BlackbirdStandalone/ToothEater-HW-THT/pcb/BOM/v1.1/BOM.png

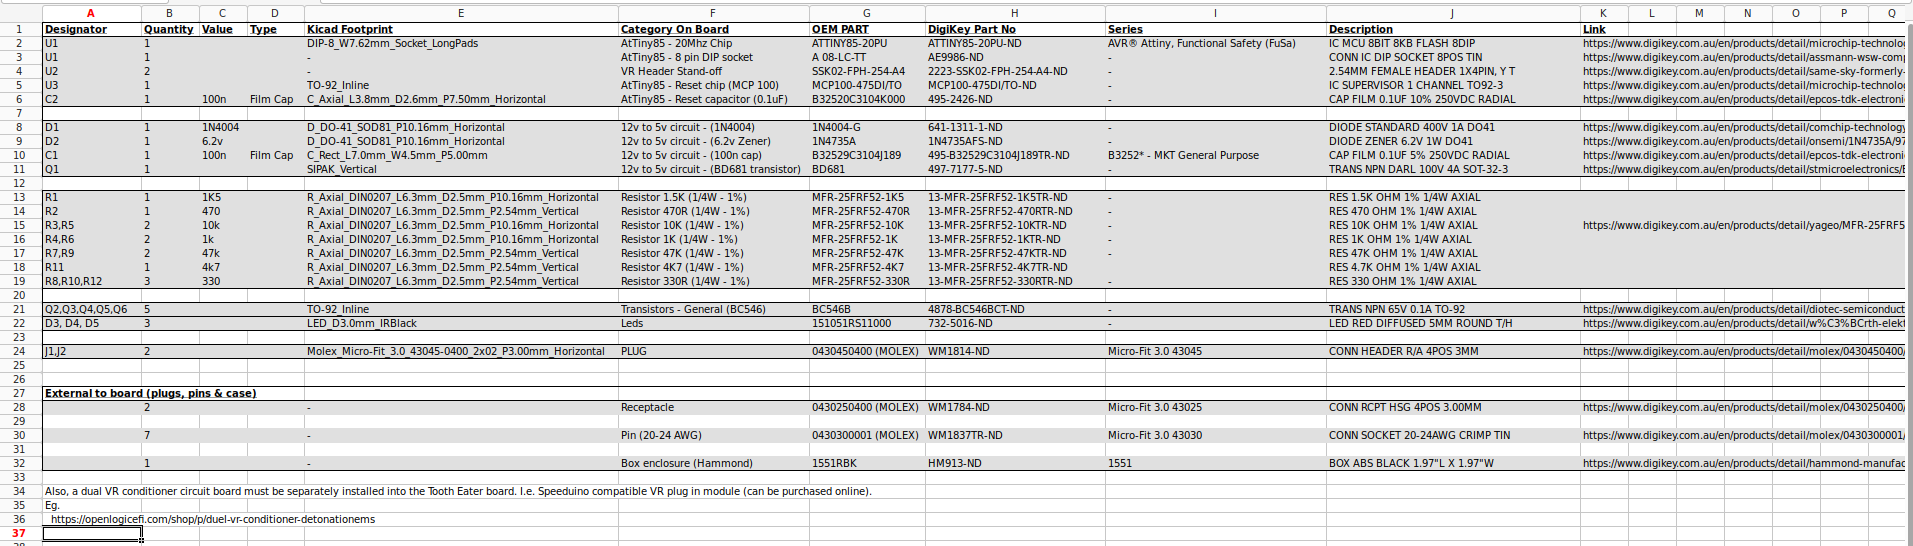
pcb/BOM/v1.1/BOM.png
